DADDesign-Projects/PENDA-Hardware/Images/PENDA3.png

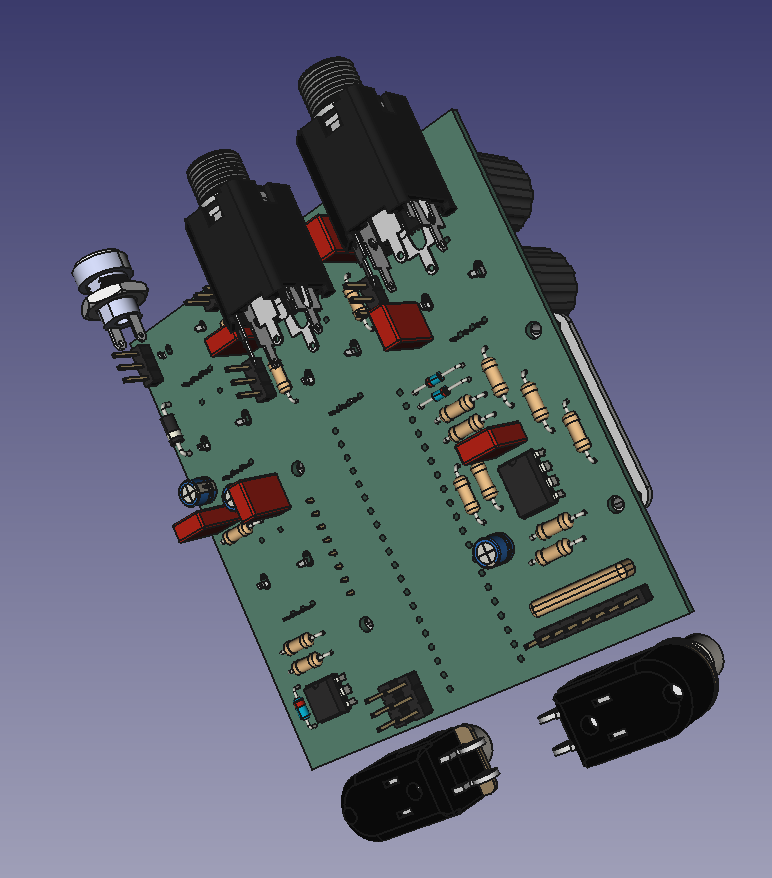
Images/PENDA3.png
